S-March/smarchWatch_Public/Software/smarchWatch_DA14683/DA1468x_SDK_1.0.14.1081/DA1468x_DA15xxx_SDK_1.0.14.1081/projects/dk_apps/ble_profiles/smarchWatch/displayFonts.h

/*
 * displayFonts.h
 *
 *  Created on: Jan 25, 2019
 *      Author: samsonm
 */

#ifndef DISPLAYFONTS_H_
#define DISPLAYFONTS_H_

#define FONT_CHARACTER_WIDTH 15
#define FONT_CHARACTER_HEIGHT 25
#define FONT_CHARACTERS_COLUMNS 13
#define FONT_CHARACTERS_ROWS 6

int displayDrawCharacter(int X_START, int Y_START, char CHARACTER);
void displayDrawString(int X_START, int Y_START, int KERNING_SIZE, int MARGIN, int POINTER_TO_STRING);
int setCircularMargin(int CURRENT_Y_POSITION);

#endif /* DISPLAYFONTS_H_ */
