S-March/smarchWatch_Public/Software/smarchWatch_DA14683/DA1468x_SDK_1.0.14.1081/DA1468x_DA15xxx_SDK_1.0.14.1081/projects/dk_apps/ble_profiles/smarchWatch/imageOffsets.h

/*
 * imageOffsets.h
 *
 *  Created on: Jan 23, 2019
 *      Author: samsonm
 */

#ifndef IMAGEOFFSETS_H_
#define IMAGEOFFSETS_H_

#define WATCH_FACE_OFFSET 0
#define TZIPI_OFFSET 115202
#define NEW_MESSAGE_OFFSET 230404
#define NEW_MAIL_OFFSET 261606
#define MARISSA_OFFSET 292808
#define HOME_OFFSET 408010
#define FONT_OFFSET 523212

#define TOTAL_MEMORY_USED 582014
#define TOTAL_MEMORY_AVAILABLE 16195202
#define TOTAL_MEMORY_PERCENT USED 3
//Time to load all data at 115200 baud: 40 seconds

#endif /* IMAGEOFFSETS_H_ */
